Sylvia3366/leebyte/case/Bottom Case Model/Btm_case1.png

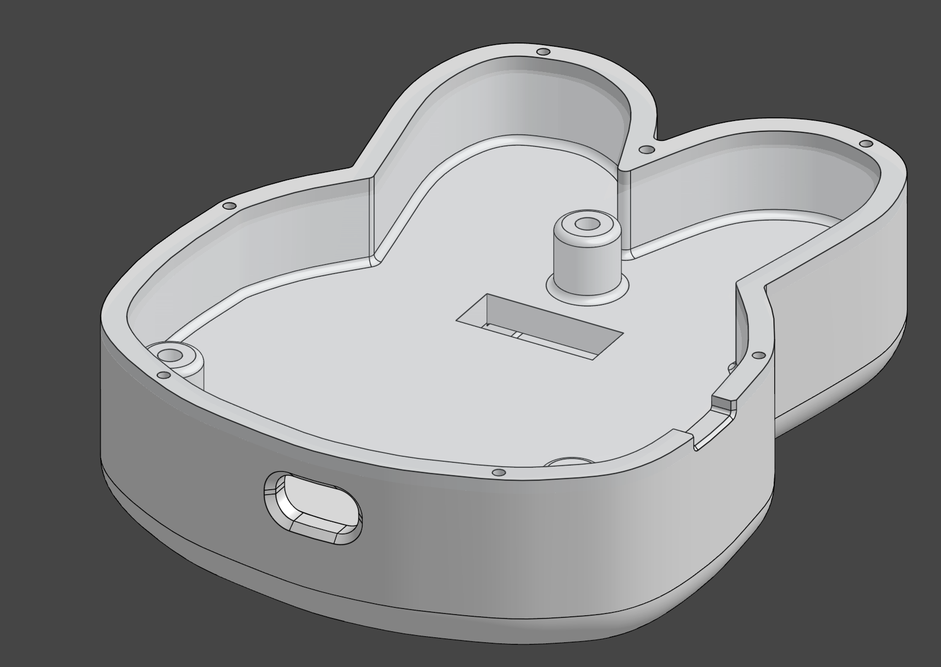
case/Bottom Case Model/Btm_case1.png
