Sylvia3366/leebyte/case/Button Cap Model/Button1.png

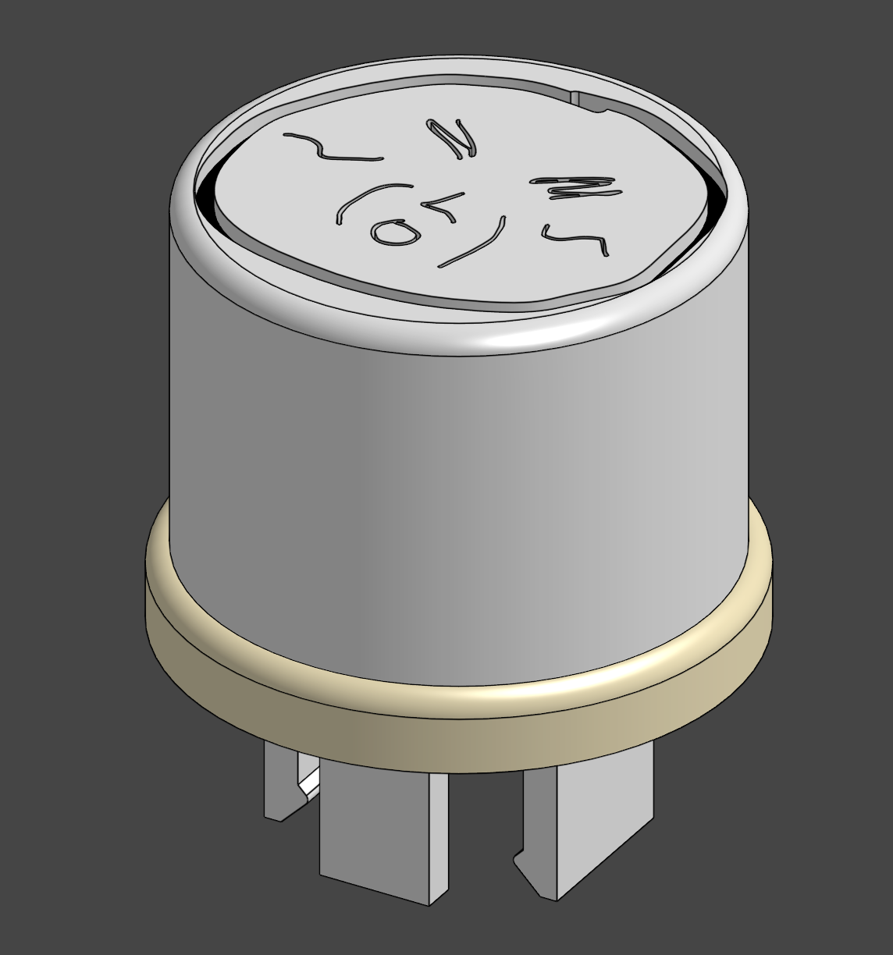
case/Button Cap Model/Button1.png
