Sylvia3366/leebyte/case/CAD/128x64 OLED Model/OLED.png

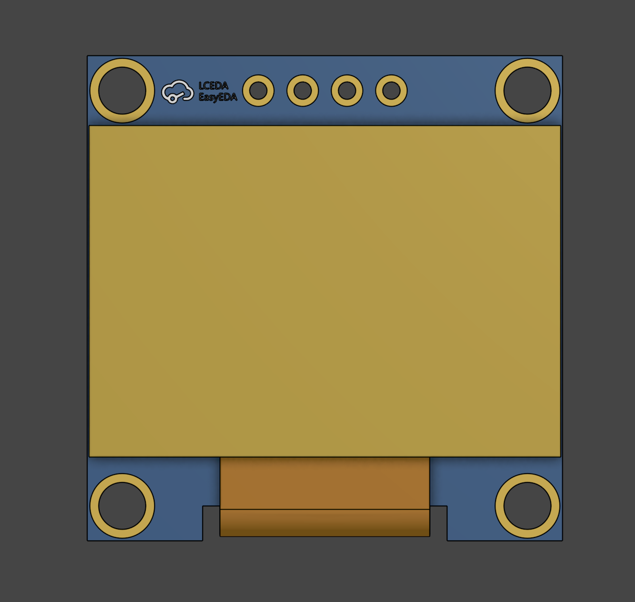
case/CAD/128x64 OLED Model/OLED.png
