Sylvia3366/leebyte/case/CAD/Seeed Studio XIAO ESP32 C3 Model/seeed2.png

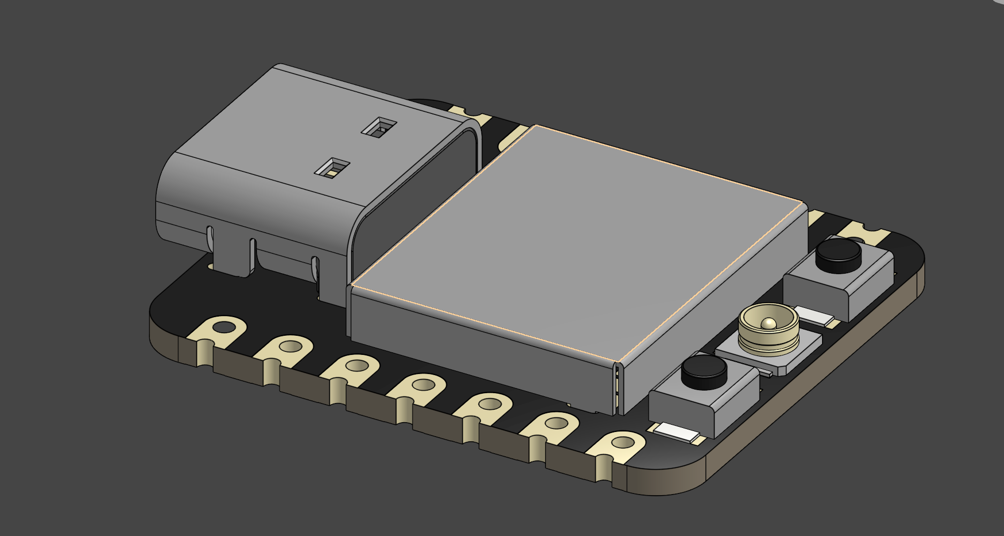
case/CAD/Seeed Studio XIAO ESP32 C3 Model/seeed2.png
