Sylvia3366/leebyte/case/Top Case Model/Top_case1.png

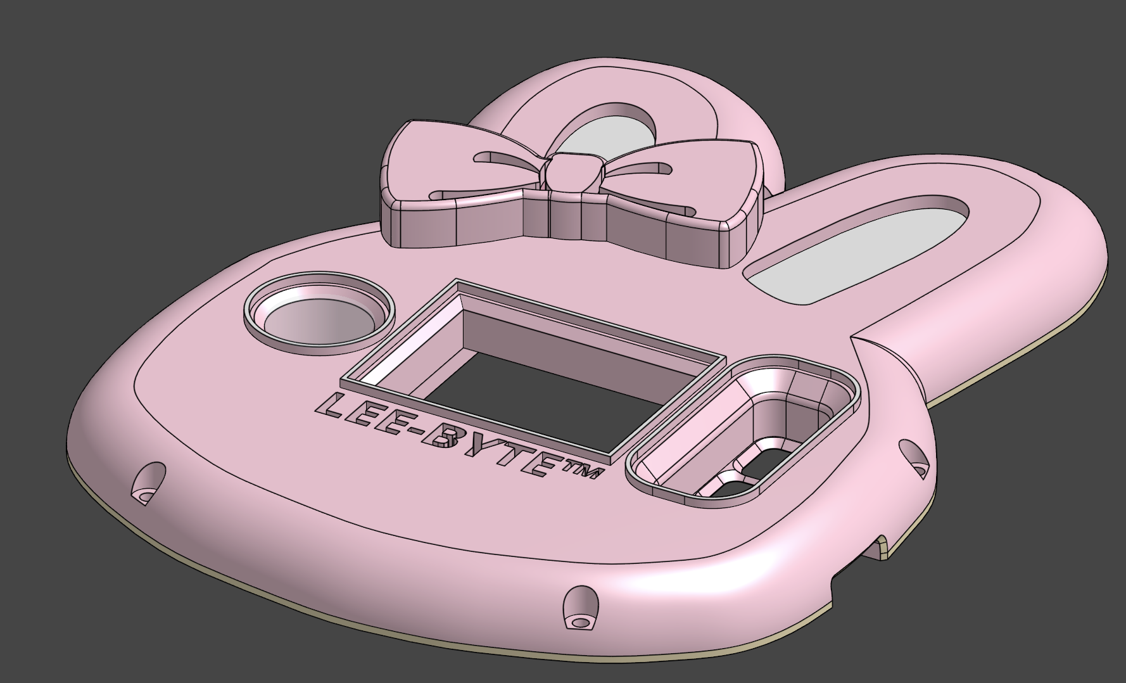
case/Top Case Model/Top_case1.png
