Sylvia3366/leebyte/case/Top Case Model/Top_case.png

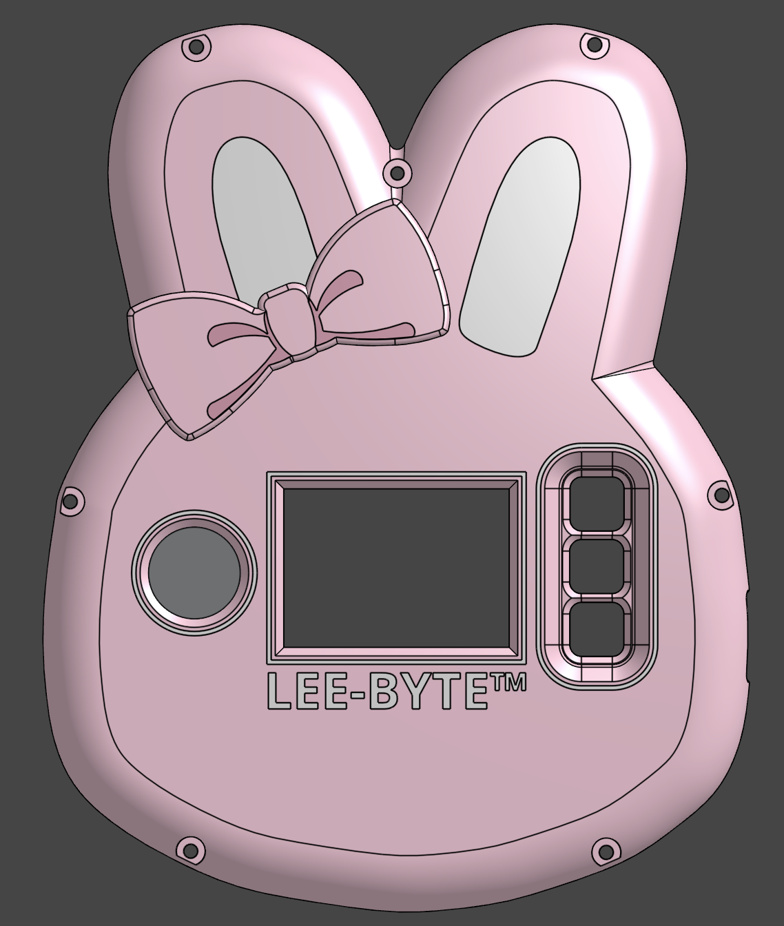
case/Top Case Model/Top_case.png
