Sylvia3366/leebyte/case/CAD/Slide Switch Model/Slide Switch.step

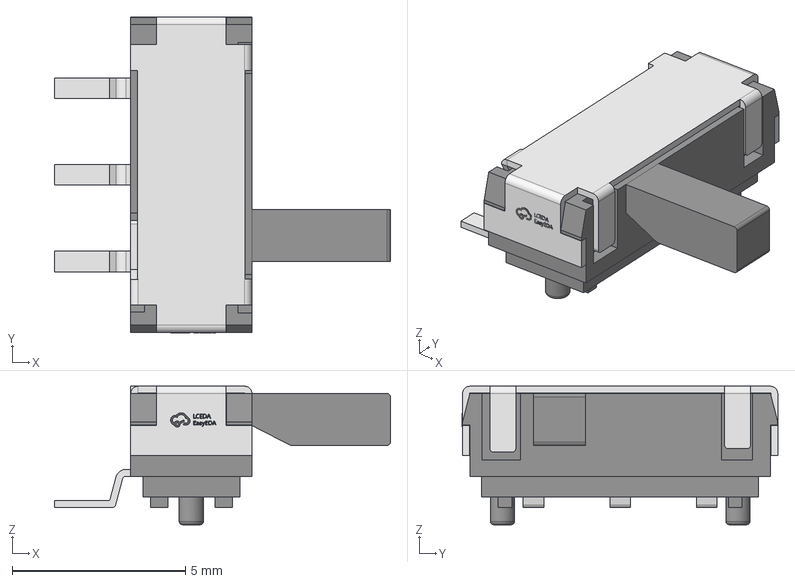
[picture p27: CAD file, 2026-06-16]
case/CAD/Slide Switch Model/Slide Switch.step
9.70 x 9.11 x 4.00 mm
SW-SMD_MST-12D18G4-SPDT-SLIDE-SWITCH x 2
