Sylvia3366/leebyte/case/CAD/Tact Switch Model/SW-TH_4P-L4.5-W4.5-P3.00-LS4.8 (1).step

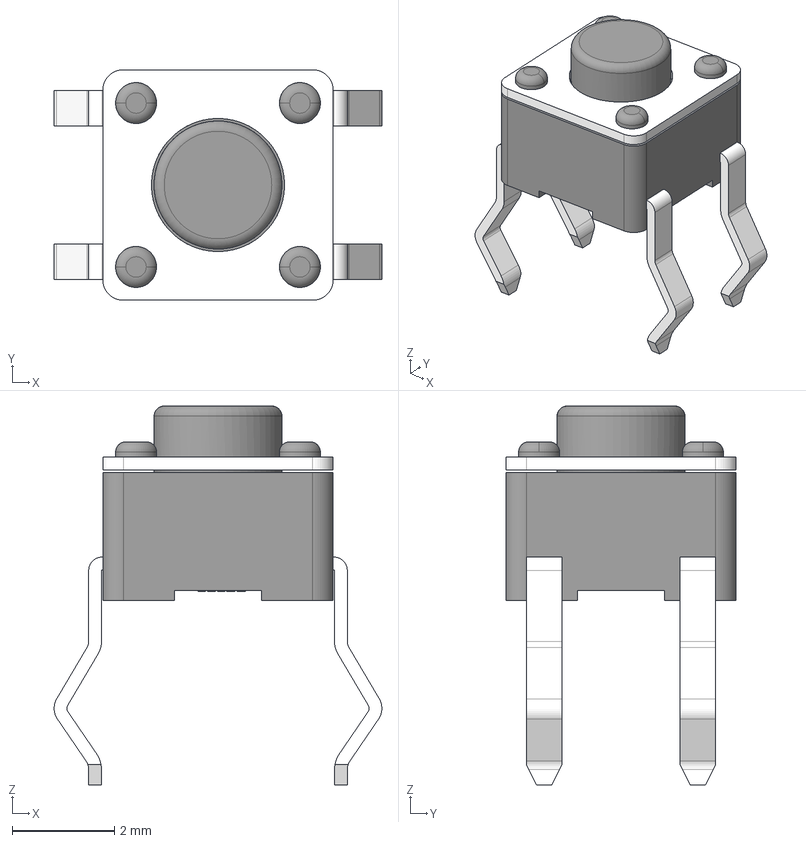
[picture p28: CAD file, 2026-06-16]
case/CAD/Tact Switch Model/SW-TH_4P-L4.5-W4.5-P3.00-LS4.8 (1).step
6.40 x 4.50 x 7.40 mm
