Sylvia3366/leebyte/case/CAD/M1.6x0.35mm 6mm Screw Model/PZ Pan head screw M1.6x0.35 x 6.stl

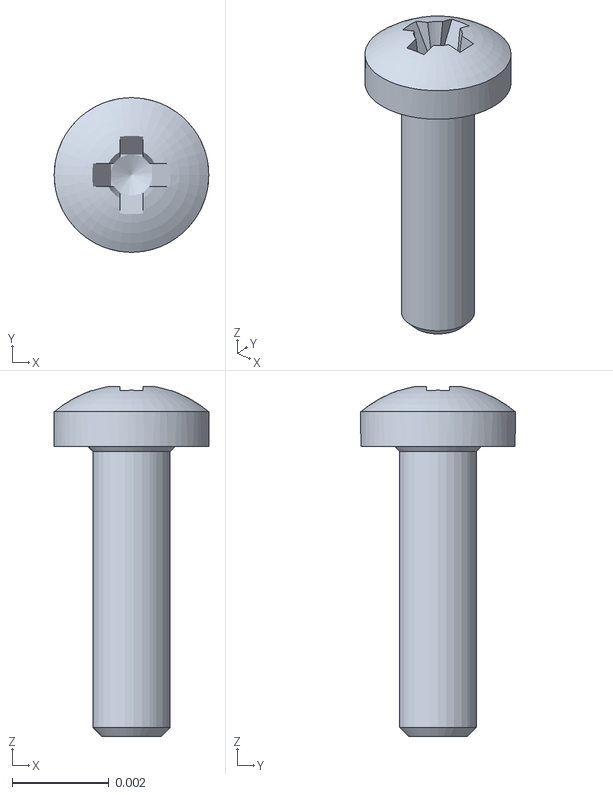
[picture p29: CAD file, 2026-06-16]
case/CAD/M1.6x0.35mm 6mm Screw Model/PZ Pan head screw M1.6x0.35 x 6.stl
0.0032 x 0.0032 x 0.00724
