Sylvia3366/leebyte/case/CAD/M2 4mm Standoff Model/M2 x 5 across flats 4mm.step

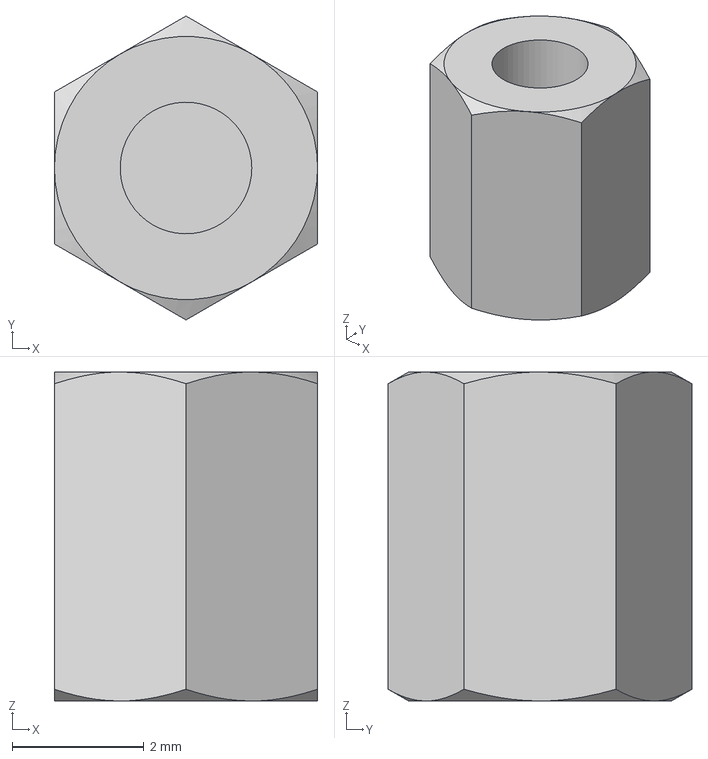
[picture p30: CAD file, 2026-06-16]
case/CAD/M2 4mm Standoff Model/M2 x 5 across flats 4mm.step
4.00 x 4.62 x 5.00 mm
